juanmcasillas/CatFeederPrototype/CAD/datasheets/funcion_motor_l293d.png

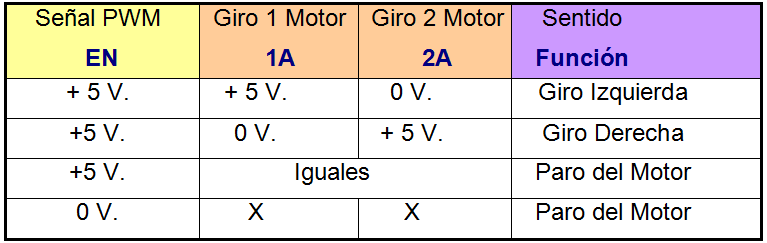
CAD/datasheets/funcion_motor_l293d.png
