juanmcasillas/CatFeederPrototype/CAD/datasheets/l293d.png

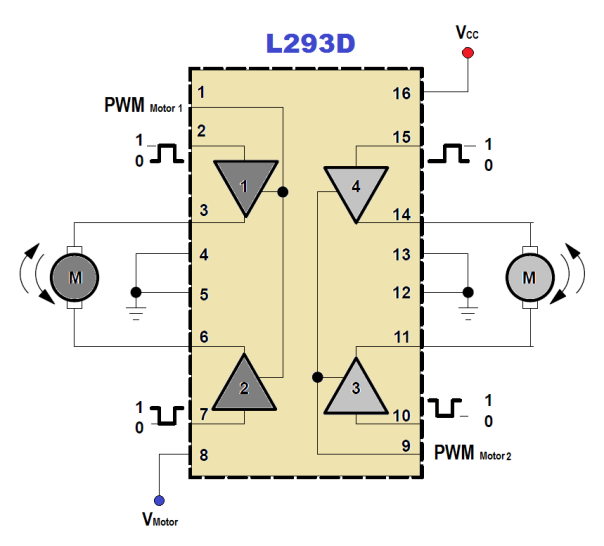
CAD/datasheets/l293d.png
