juanmcasillas/CatFeederPrototype/python/data/blue_ball.png

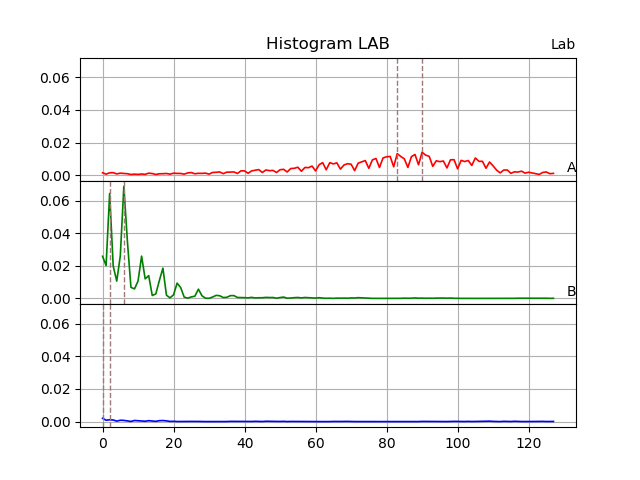
python/data/blue_ball.png
