juanmcasillas/CatFeederPrototype/python/data/eli.png

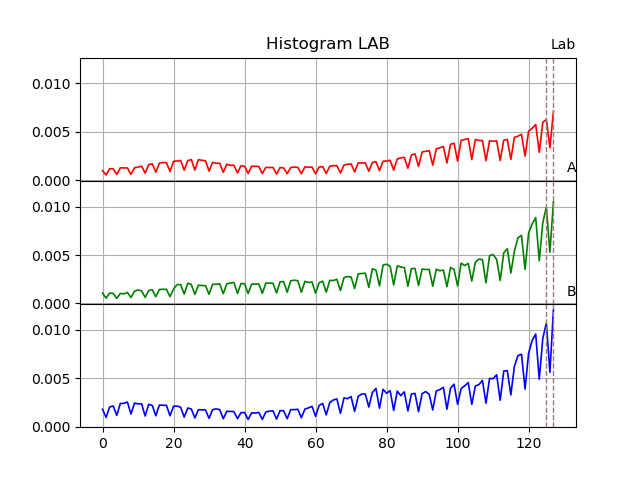
python/data/eli.png
