juanmcasillas/CatFeederPrototype/python/data/firulais.png

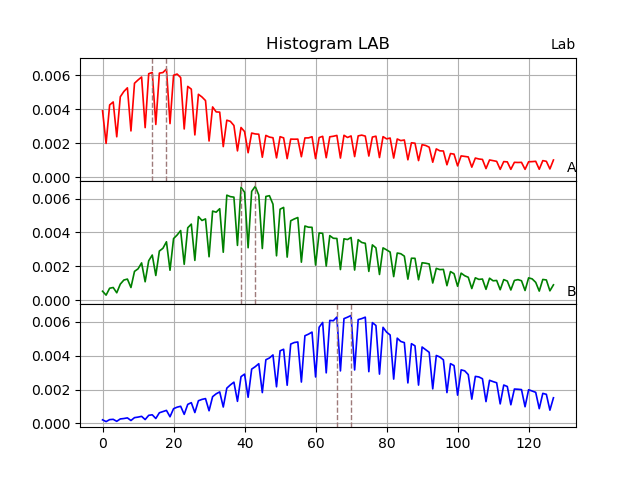
python/data/firulais.png
