juanmcasillas/CatFeederPrototype/python/webserver/www/photos/trans/eli.png

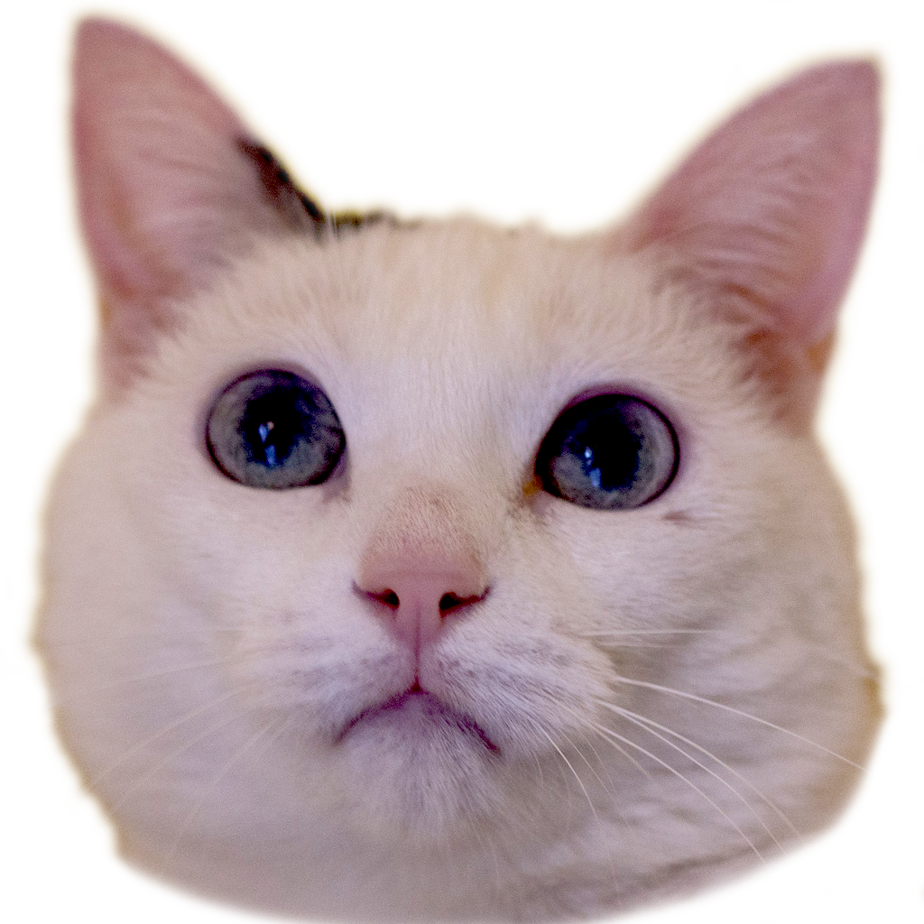
python/webserver/www/photos/trans/eli.png
