juanmcasillas/CatFeederPrototype/python/webserver/www/photos/trans/firulais.png

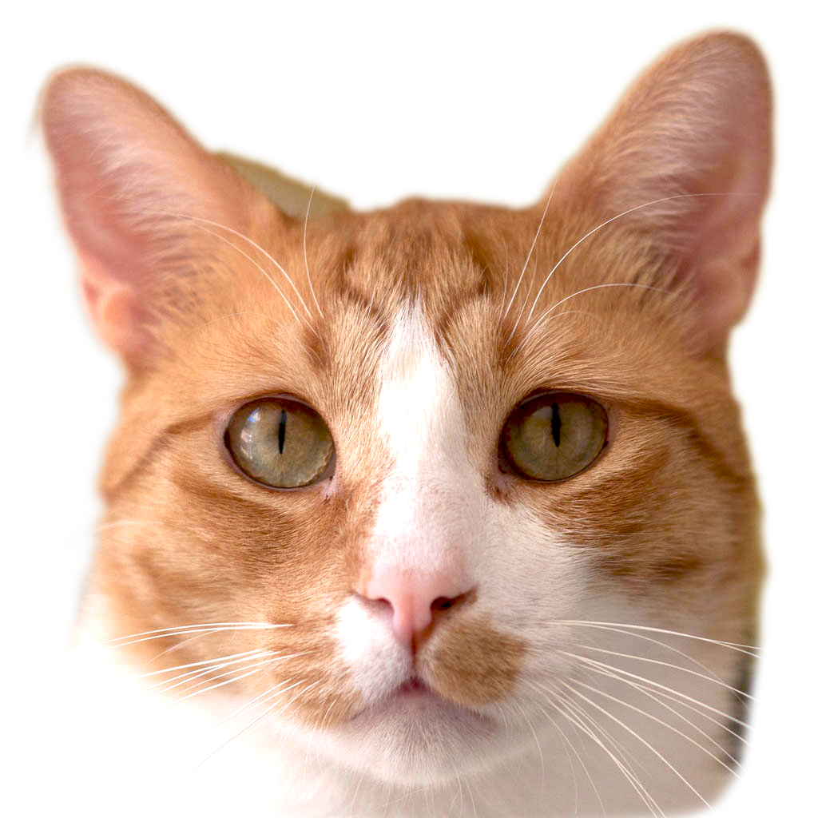
python/webserver/www/photos/trans/firulais.png
