juanmcasillas/CatFeederPrototype/python/webserver/www/snaps/2017/09/15/1505491956.jpg

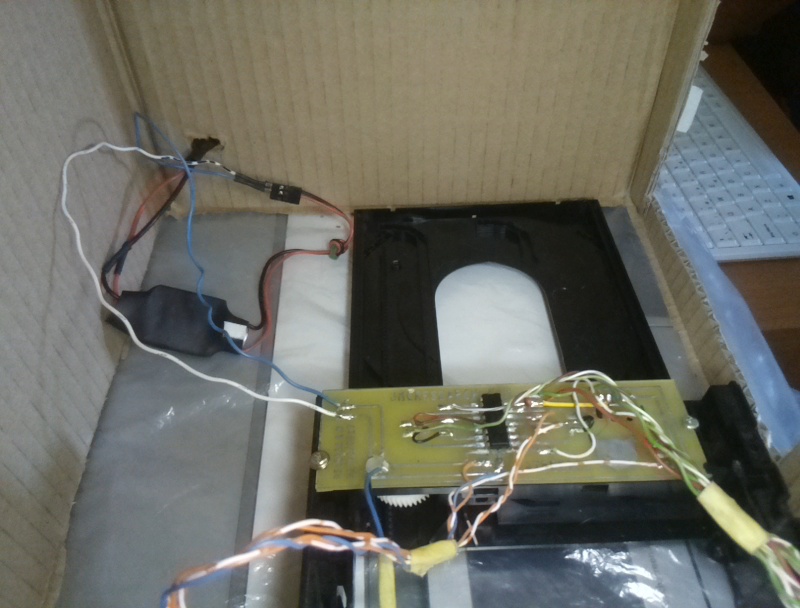
python/webserver/www/snaps/2017/09/15/1505491956.jpg
