juanmcasillas/CatFeederPrototype/python/webserver/www/snaps/2017/09/15/1505492081.jpg

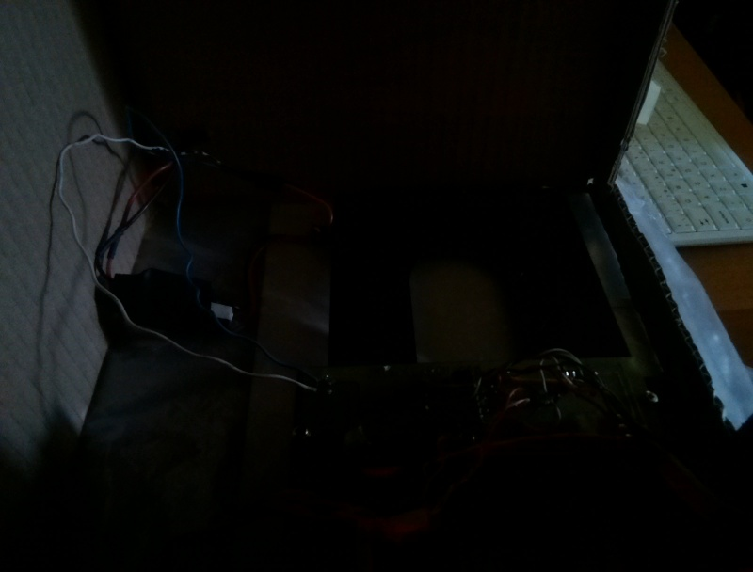
python/webserver/www/snaps/2017/09/15/1505492081.jpg
