juanmcasillas/CatFeederPrototype/python/webserver/www/snaps/2017/09/15/1505498070.jpg

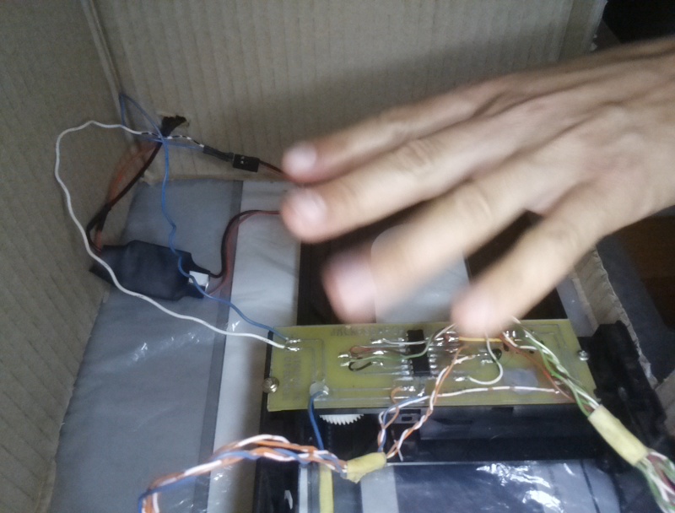
python/webserver/www/snaps/2017/09/15/1505498070.jpg
