juanmcasillas/CatFeederPrototype/python/webserver/www/snaps/2017/09/15/1505506237.jpg

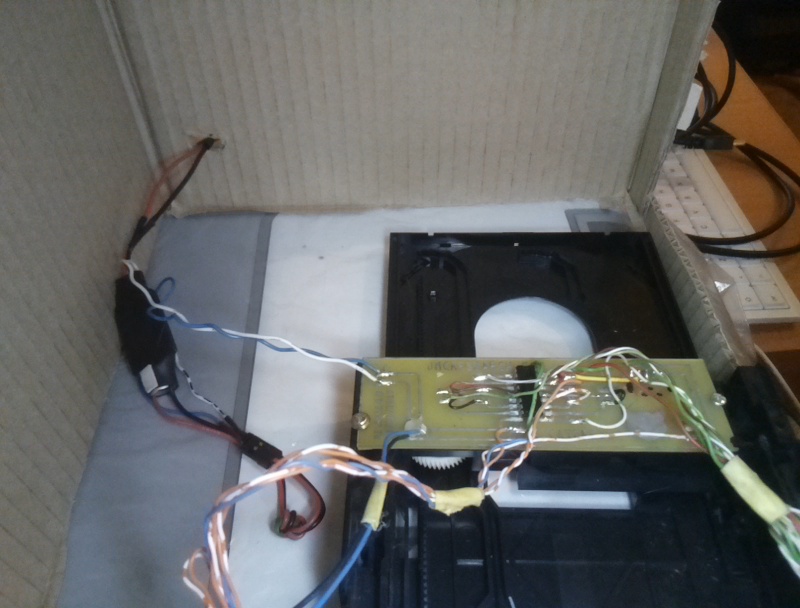
python/webserver/www/snaps/2017/09/15/1505506237.jpg
