juanmcasillas/CatFeederPrototype/python/webserver/www/snaps/2017/09/15/1505513970.jpg

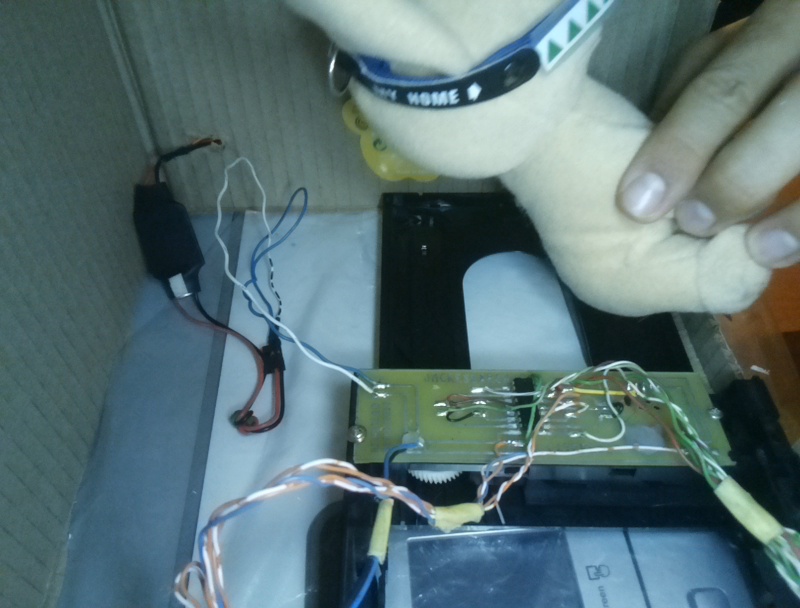
python/webserver/www/snaps/2017/09/15/1505513970.jpg
