juanmcasillas/CatFeederPrototype/python/webserver/www/snaps/2017/09/15/1505515217.jpg

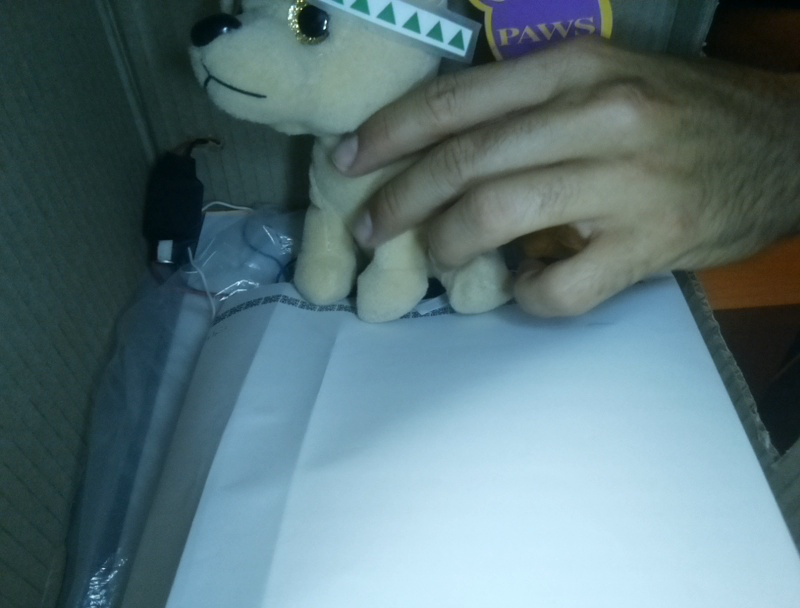
python/webserver/www/snaps/2017/09/15/1505515217.jpg
