juanmcasillas/CatFeederPrototype/python/webserver/www/snaps/2017/09/15/1505515292.jpg

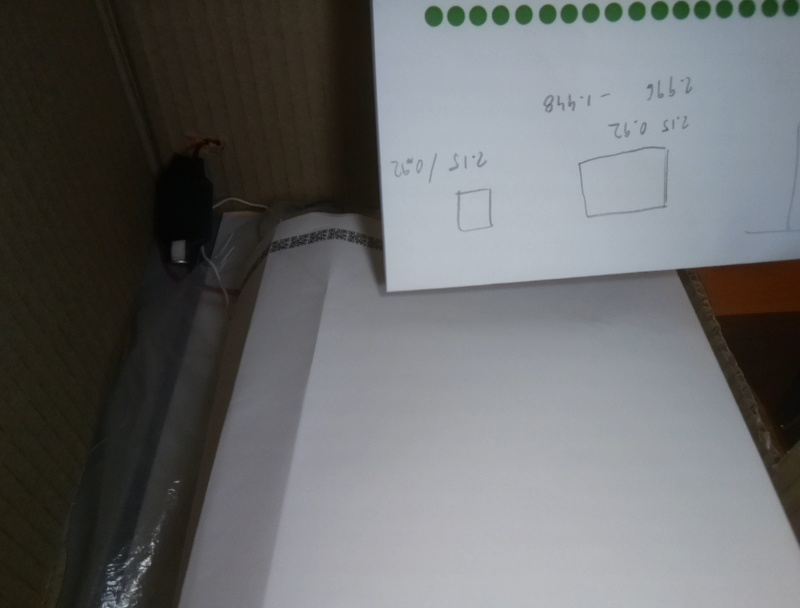
python/webserver/www/snaps/2017/09/15/1505515292.jpg
