juanmcasillas/CatFeederPrototype/python/webserver/www/snaps/2017/09/18/1505749713.jpg

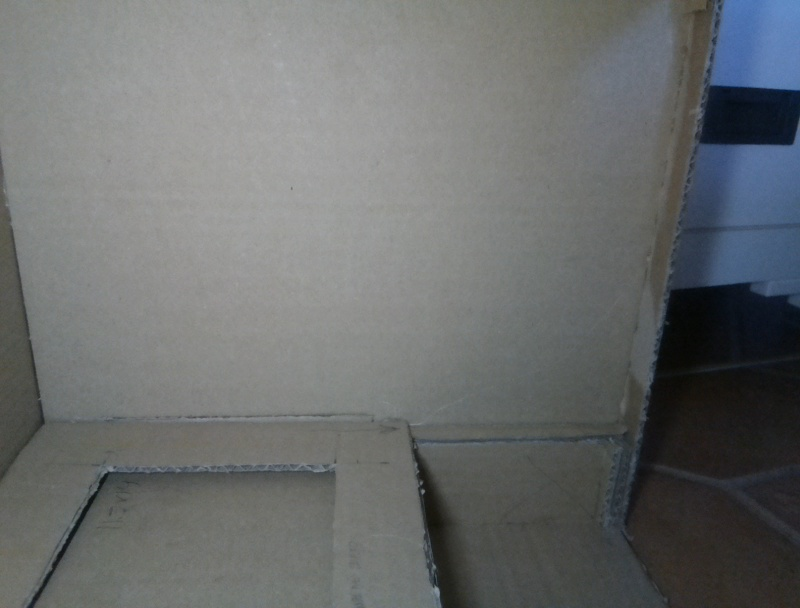
python/webserver/www/snaps/2017/09/18/1505749713.jpg
