juanmcasillas/CatFeederPrototype/python/webserver/www/snaps/2017/10/12/1507797755.png

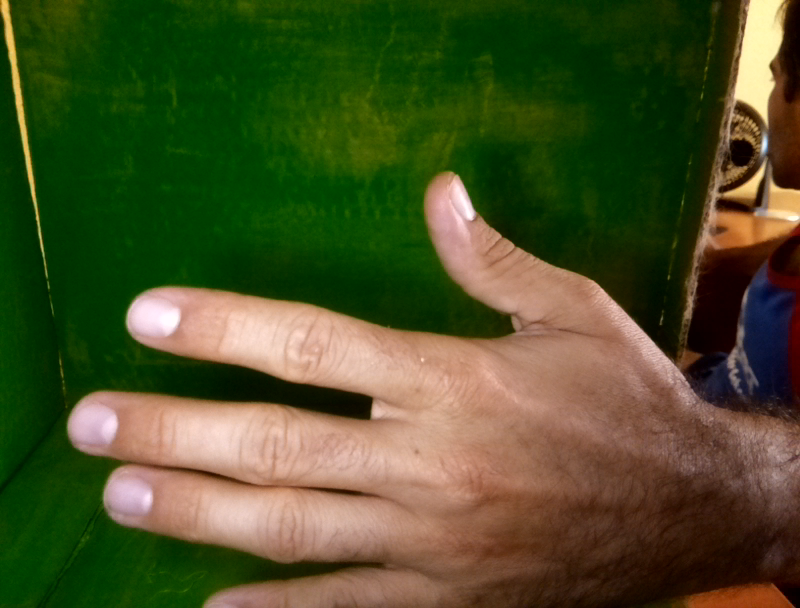
python/webserver/www/snaps/2017/10/12/1507797755.png
