juanmcasillas/CatFeederPrototype/python/webserver/www/snaps/2017/10/12/1507801003.png

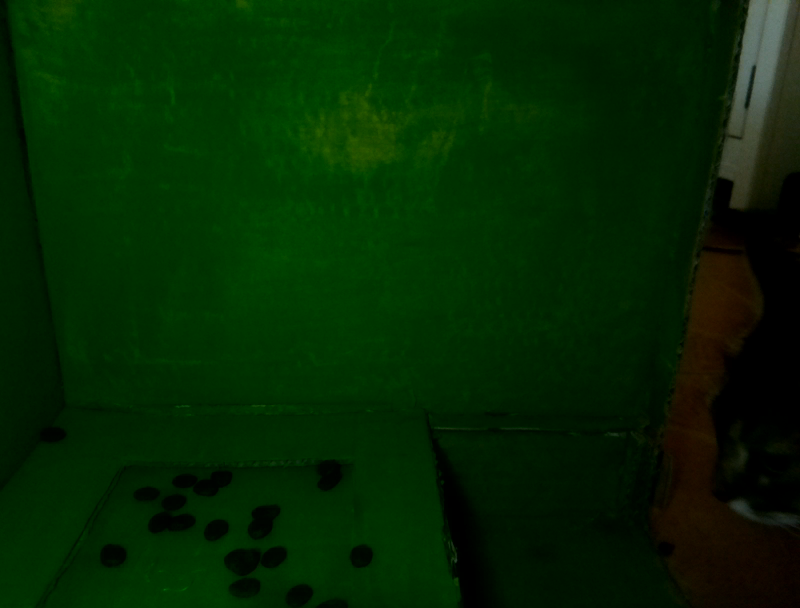
python/webserver/www/snaps/2017/10/12/1507801003.png
