juanmcasillas/CatFeederPrototype/python/webserver/www/snaps/2017/10/12/1507808265.png

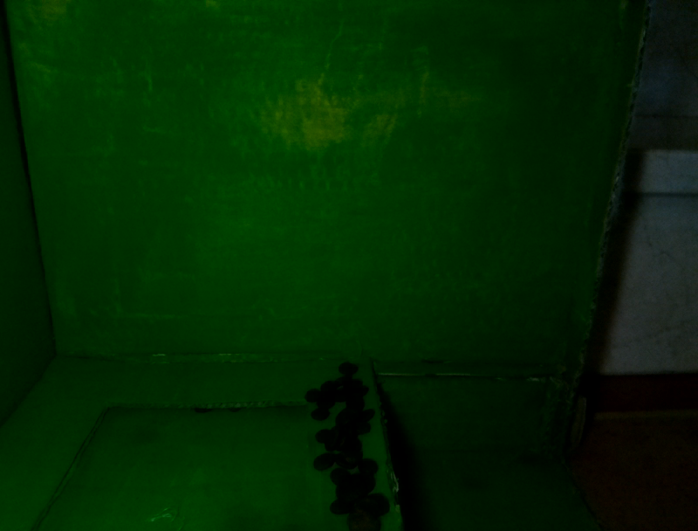
python/webserver/www/snaps/2017/10/12/1507808265.png
