juanmcasillas/CatFeederPrototype/python/webserver/www/snaps/2017/10/12/1507814186.png

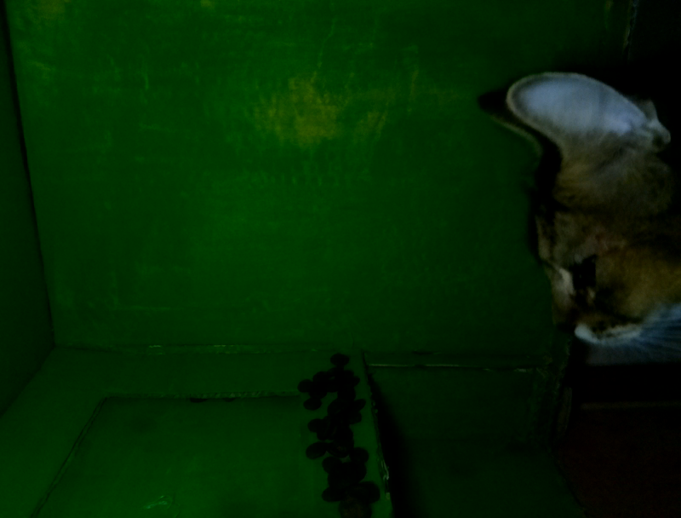
python/webserver/www/snaps/2017/10/12/1507814186.png
