juanmcasillas/CatFeederPrototype/python/webserver/www/snaps/2017/10/12/1507814691.png

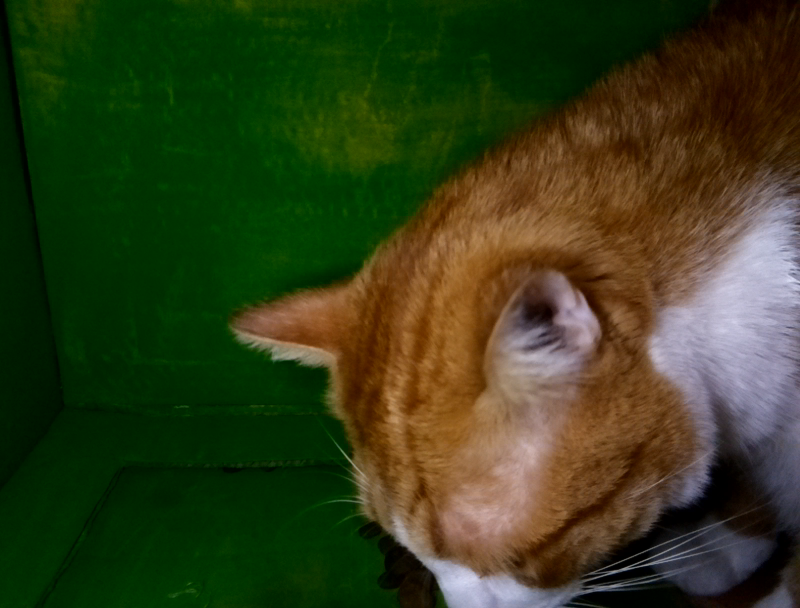
python/webserver/www/snaps/2017/10/12/1507814691.png
