juanmcasillas/CatFeederPrototype/python/webserver/www/snaps/2017/10/12/1507835978.png

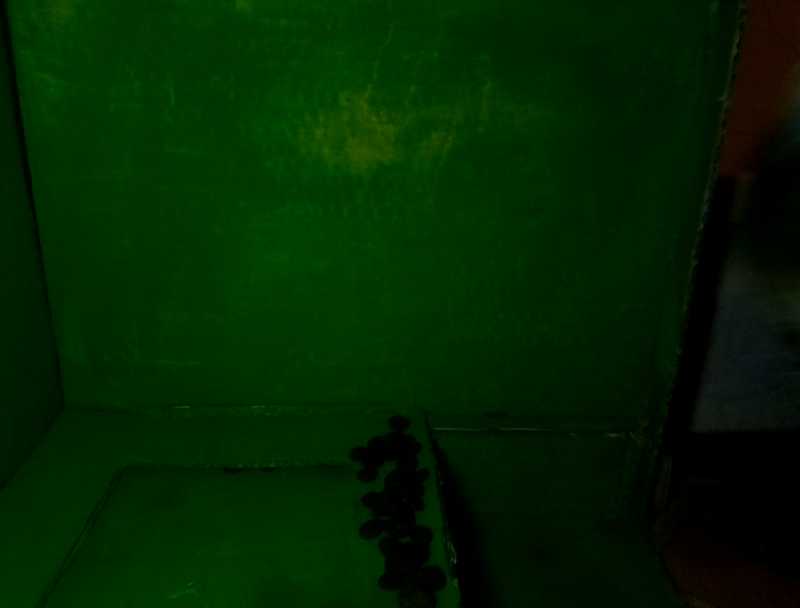
python/webserver/www/snaps/2017/10/12/1507835978.png
