juanmcasillas/CatFeederPrototype/python/webserver/www/snaps/2017/10/13/1507872299.png

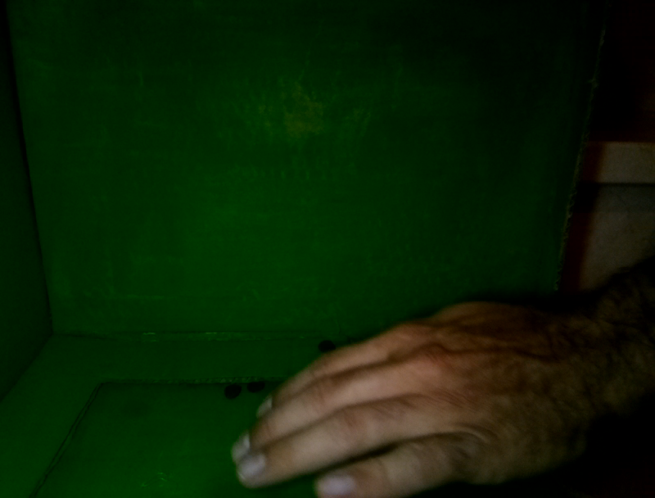
python/webserver/www/snaps/2017/10/13/1507872299.png
