juanmcasillas/CatFeederPrototype/python/webserver/www/snaps/2017/10/13/1507872304.png

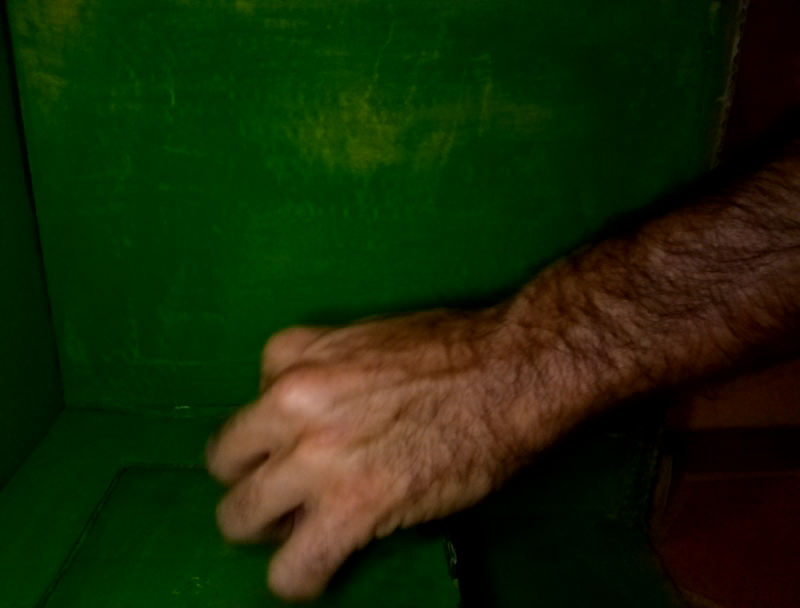
python/webserver/www/snaps/2017/10/13/1507872304.png
