juanmcasillas/CatFeederPrototype/python/webserver/www/snaps/2017/10/13/1507873627.png

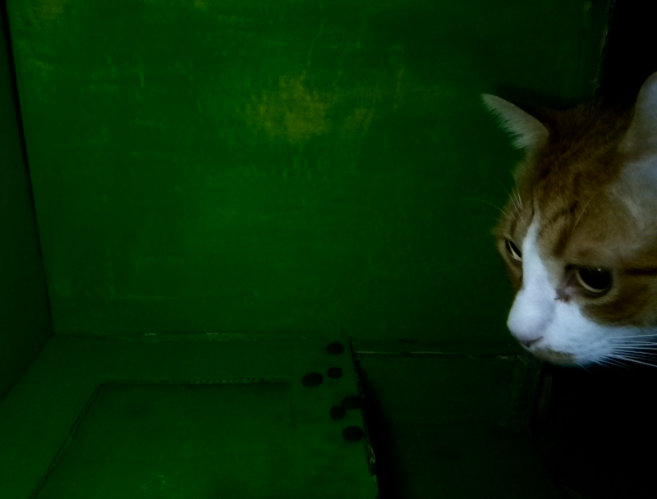
python/webserver/www/snaps/2017/10/13/1507873627.png
