juanmcasillas/CatFeederPrototype/python/webserver/www/snaps/2017/10/14/1507965277.png

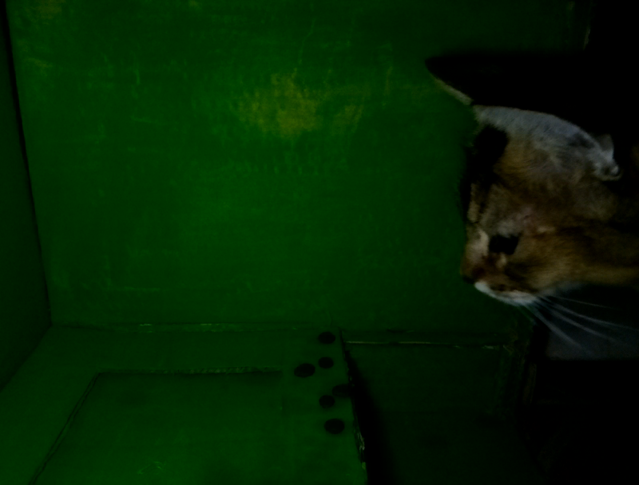
python/webserver/www/snaps/2017/10/14/1507965277.png
