juanmcasillas/CatFeederPrototype/python/webserver/www/snaps/2017/10/14/1507967059.png

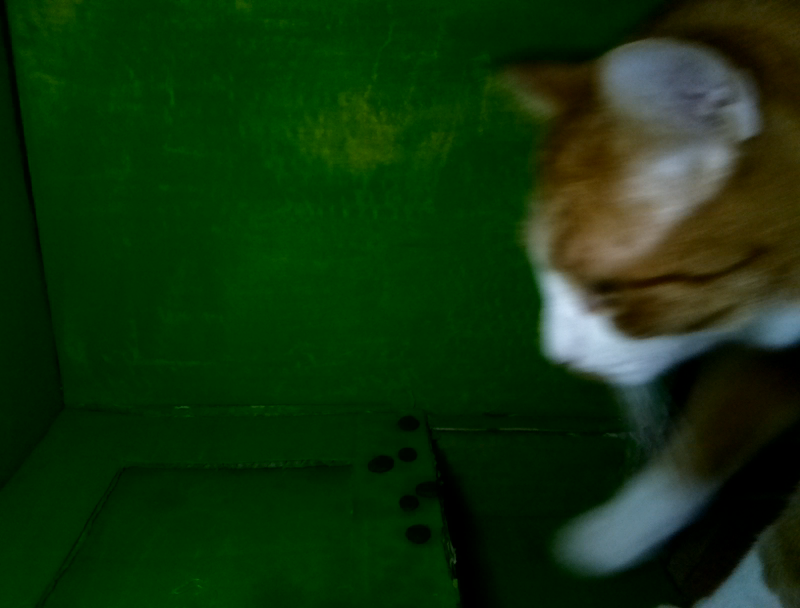
python/webserver/www/snaps/2017/10/14/1507967059.png
