juanmcasillas/CatFeederPrototype/python/webserver/www/snaps/2017/10/14/1507967062.png

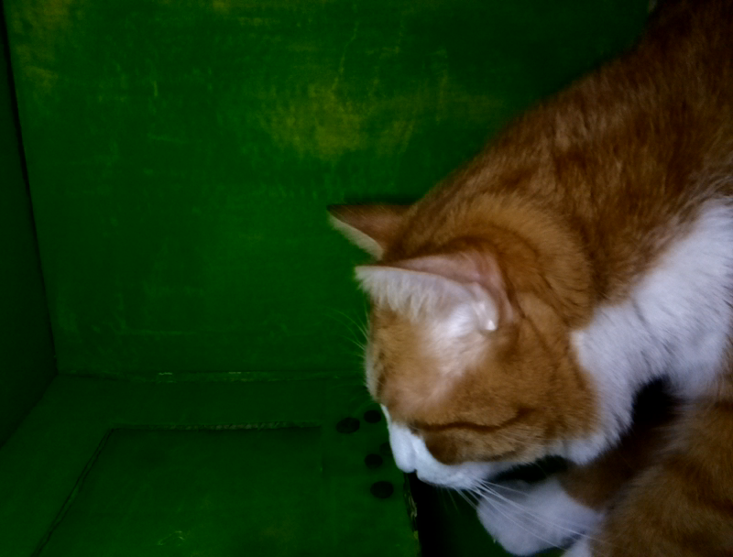
python/webserver/www/snaps/2017/10/14/1507967062.png
