juanmcasillas/CatFeederPrototype/python/webserver/www/snaps/2017/10/14/1507967931.png

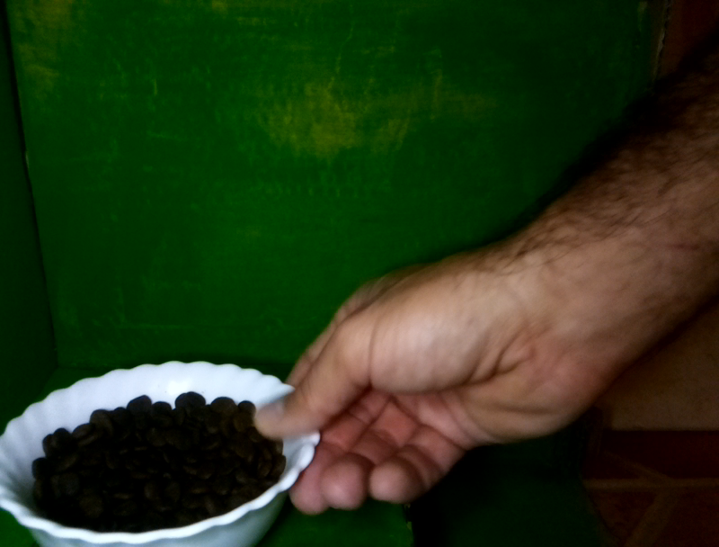
python/webserver/www/snaps/2017/10/14/1507967931.png
