juanmcasillas/CatFeederPrototype/python/webserver/www/snaps/2017/10/14/1507974870.png

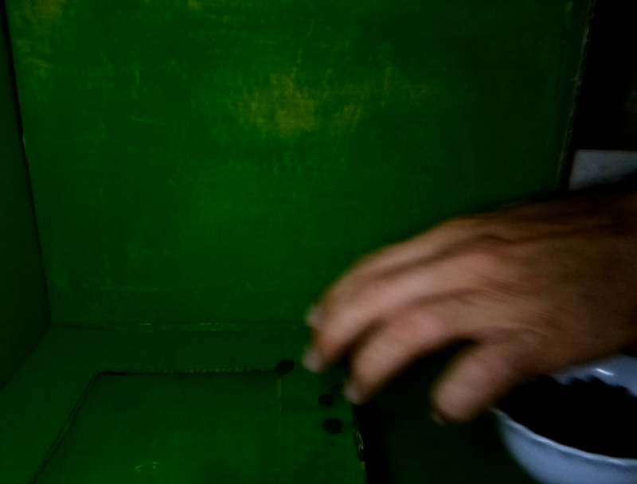
python/webserver/www/snaps/2017/10/14/1507974870.png
