juanmcasillas/CatFeederPrototype/python/webserver/www/snaps/2017/10/14/1507982404.png

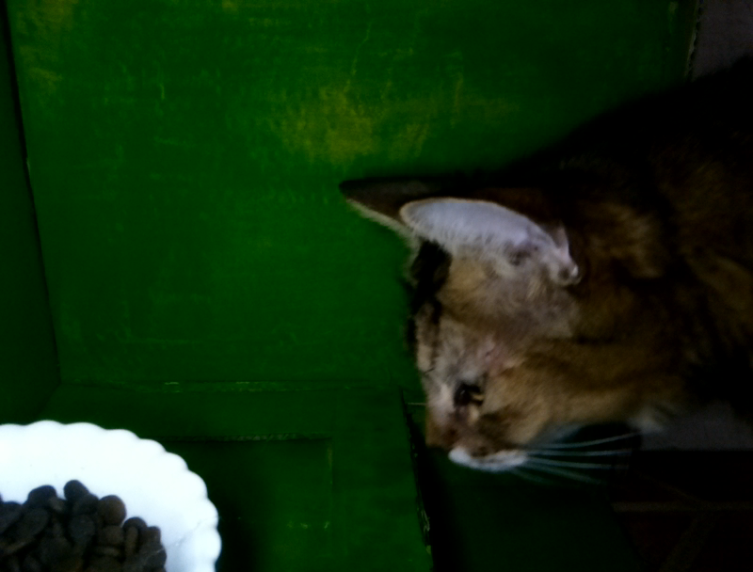
python/webserver/www/snaps/2017/10/14/1507982404.png
