juanmcasillas/CatFeederPrototype/python/webserver/www/snaps/2017/10/14/1507985400.png

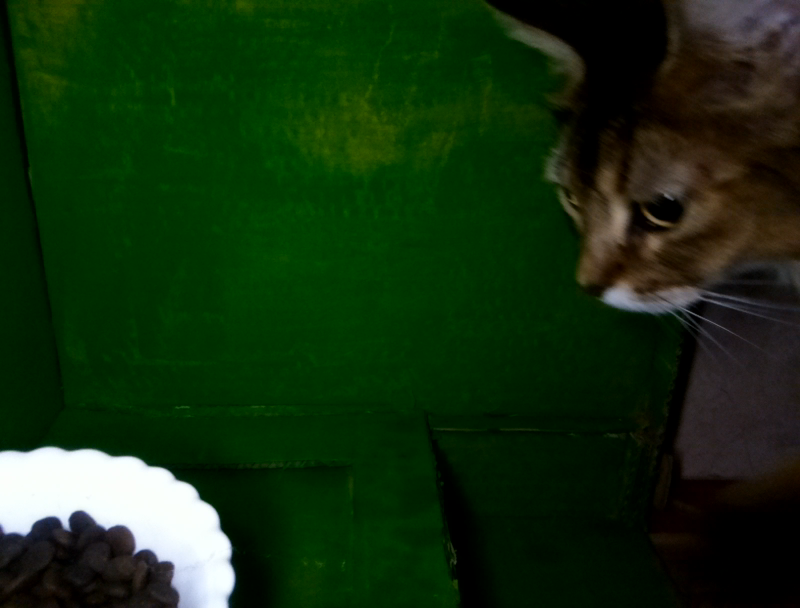
python/webserver/www/snaps/2017/10/14/1507985400.png
