juanmcasillas/CatFeederPrototype/python/webserver/www/snaps/2017/10/14/1507995303.png

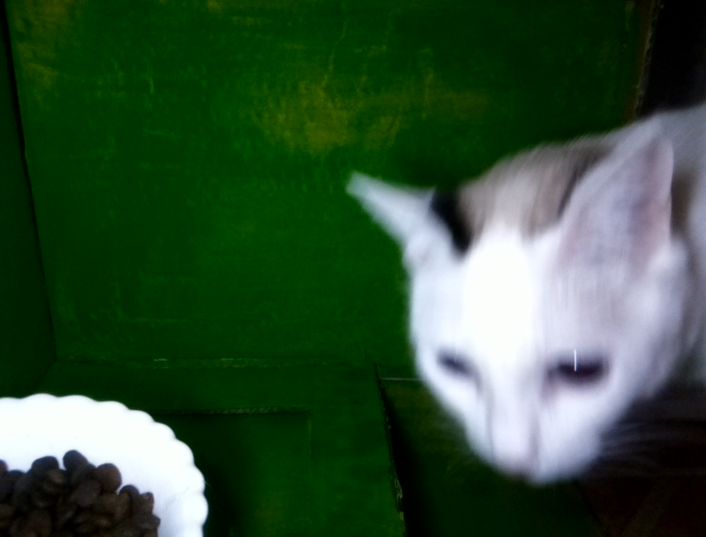
python/webserver/www/snaps/2017/10/14/1507995303.png
