juanmcasillas/CatFeederPrototype/python/webserver/www/snaps/2017/10/14/1508004973.png

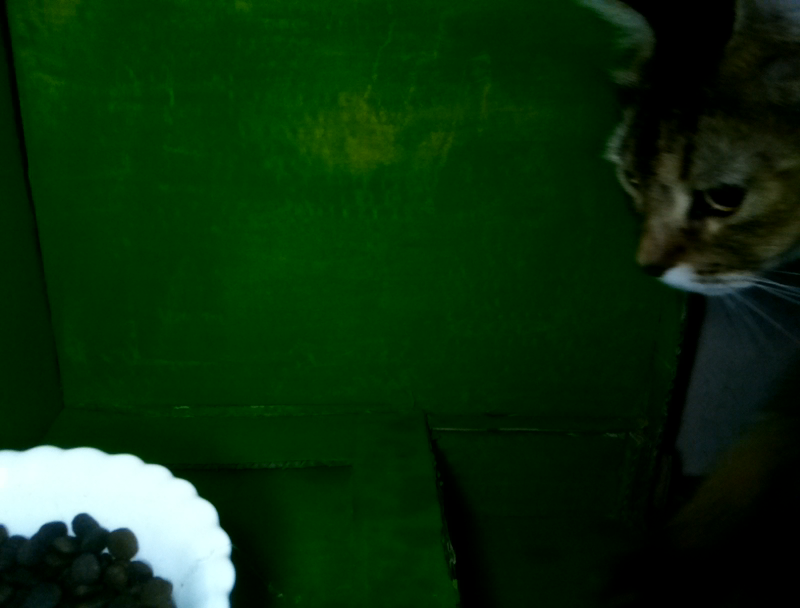
python/webserver/www/snaps/2017/10/14/1508004973.png
