juanmcasillas/CatFeederPrototype/python/webserver/www/snaps/2017/10/14/1508007424.png

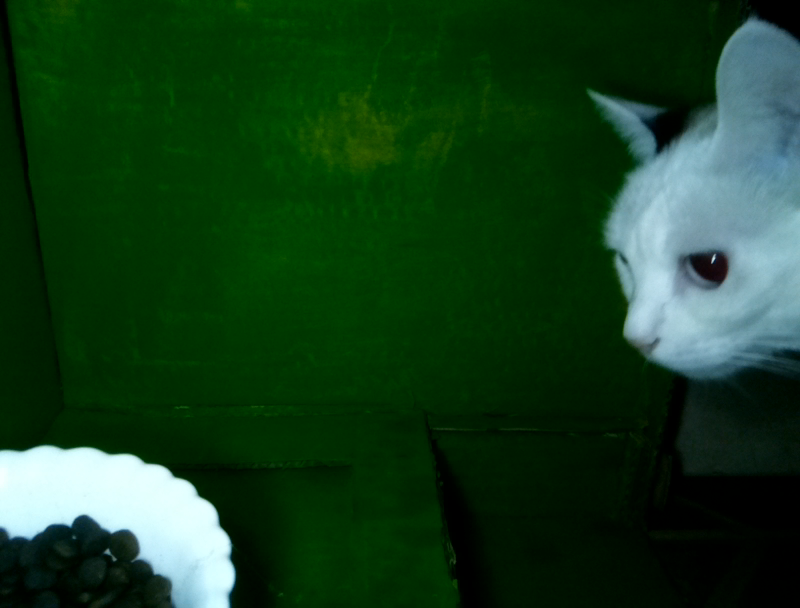
python/webserver/www/snaps/2017/10/14/1508007424.png
