juanmcasillas/CatFeederPrototype/python/webserver/www/snaps/2017/10/15/1508018659.png

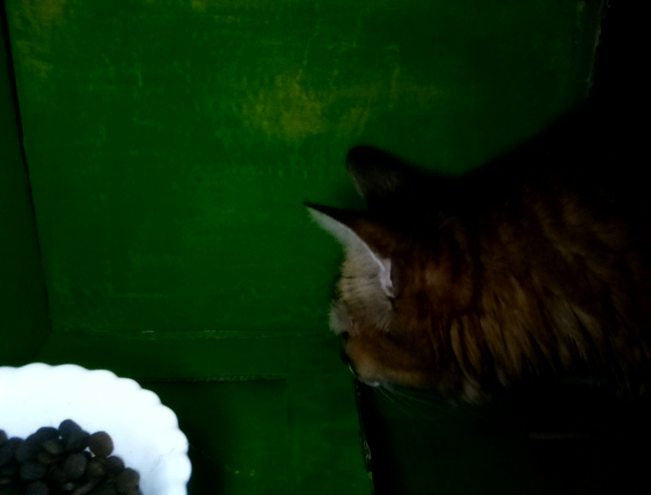
python/webserver/www/snaps/2017/10/15/1508018659.png
