juanmcasillas/CatFeederPrototype/python/webserver/www/snaps/2017/10/15/1508057400.png

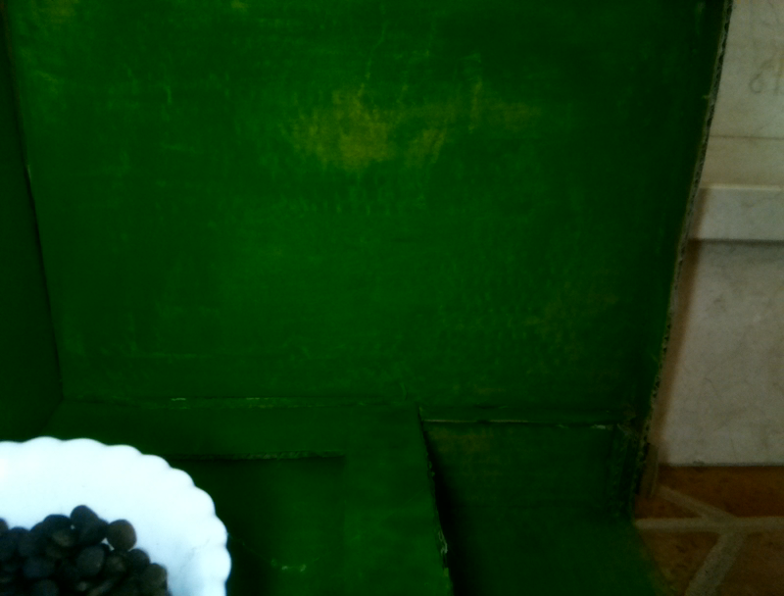
python/webserver/www/snaps/2017/10/15/1508057400.png
