juanmcasillas/CatFeederPrototype/python/webserver/www/snaps/2017/10/15/1508081175.png

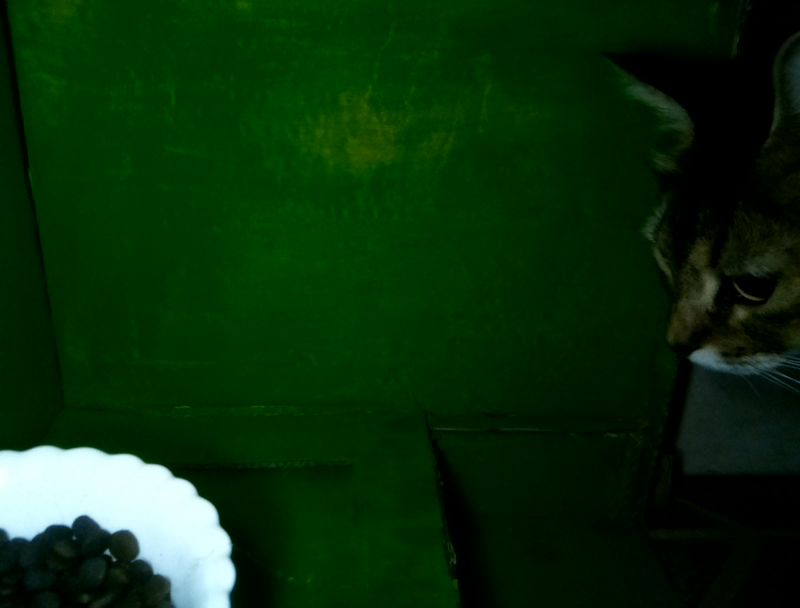
python/webserver/www/snaps/2017/10/15/1508081175.png
