juanmcasillas/CatFeederPrototype/python/webserver/www/snaps/2017/10/15/1508082414.png

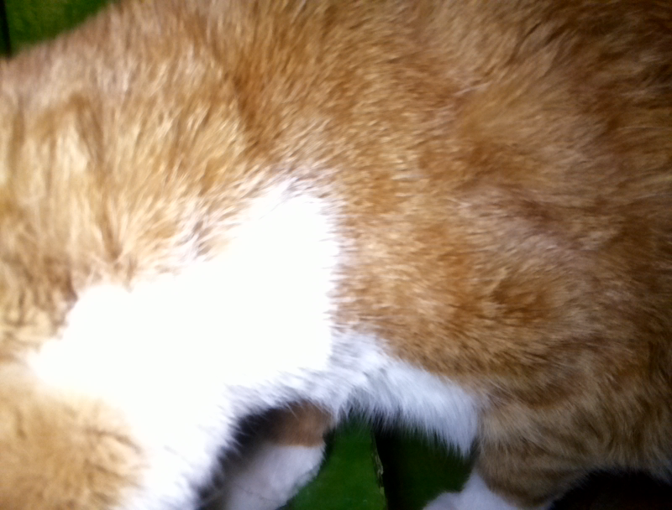
python/webserver/www/snaps/2017/10/15/1508082414.png
