juanmcasillas/CatFeederPrototype/python/webserver/www/snaps/2017/10/15/1508094019.png

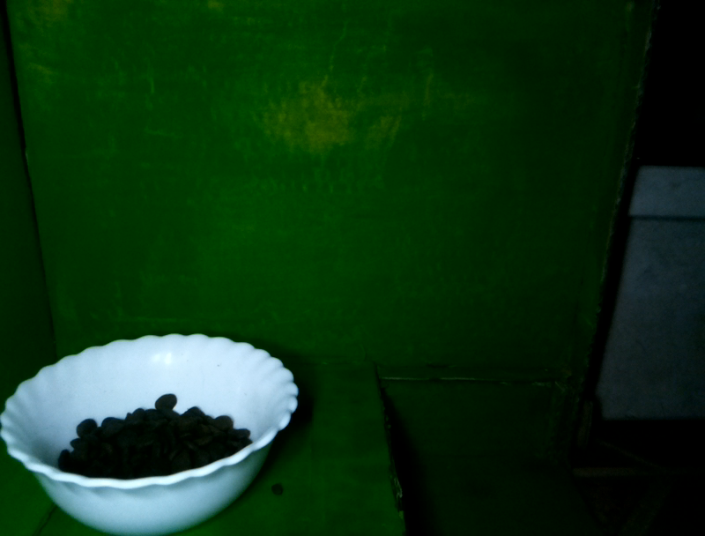
python/webserver/www/snaps/2017/10/15/1508094019.png
