juanmcasillas/CatFeederPrototype/python/webserver/www/snaps/2017/10/16/1508133024.png

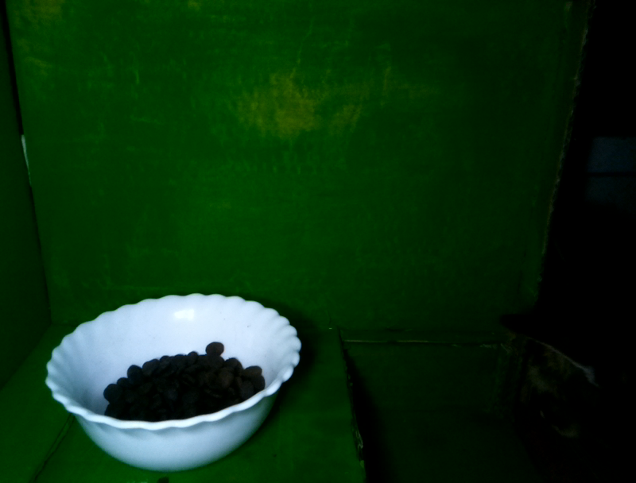
python/webserver/www/snaps/2017/10/16/1508133024.png
