juanmcasillas/CatFeederPrototype/python/webserver/www/snaps/2017/10/16/1508135601.png

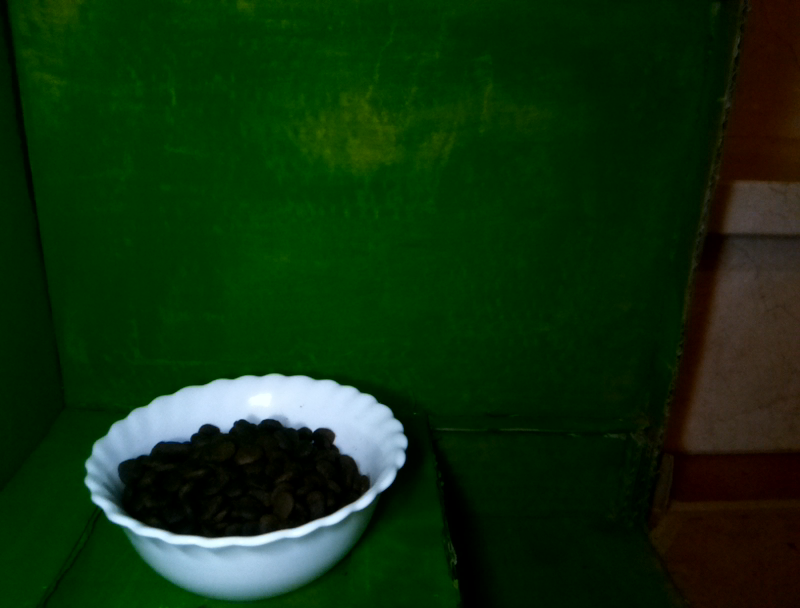
python/webserver/www/snaps/2017/10/16/1508135601.png
