juanmcasillas/CatFeederPrototype/python/webserver/www/snaps/2017/10/16/1508145276.png

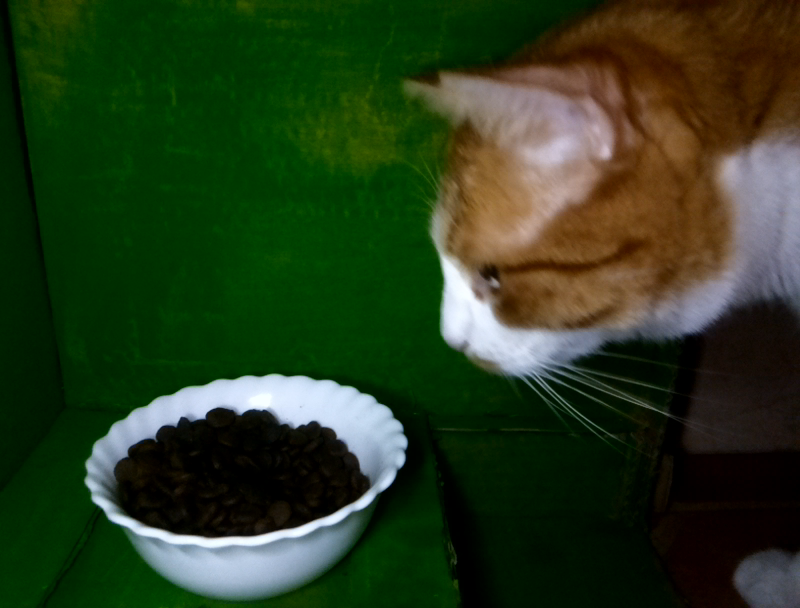
python/webserver/www/snaps/2017/10/16/1508145276.png
