juanmcasillas/CatFeederPrototype/python/webserver/www/snaps/2017/10/16/1508157271.png

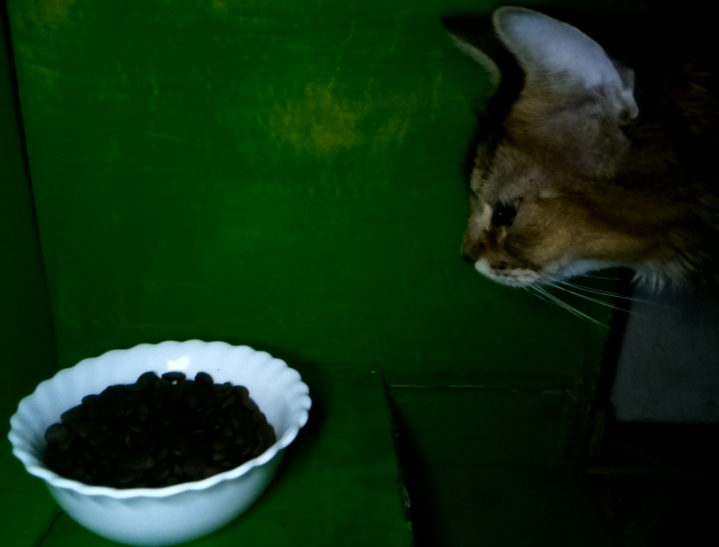
python/webserver/www/snaps/2017/10/16/1508157271.png
