juanmcasillas/CatFeederPrototype/python/webserver/www/snaps/2017/10/16/1508190802.png

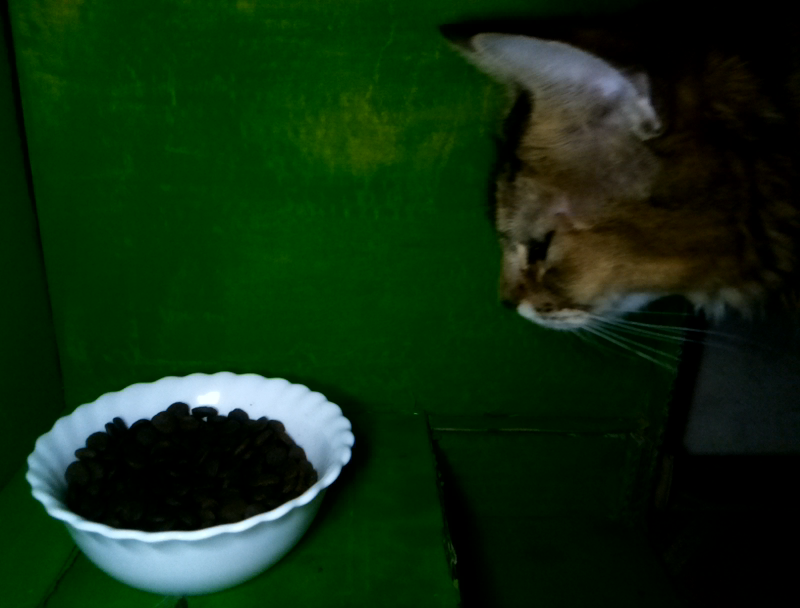
python/webserver/www/snaps/2017/10/16/1508190802.png
