juanmcasillas/CatFeederPrototype/python/webserver/www/snaps/2017/10/17/1508215944.png

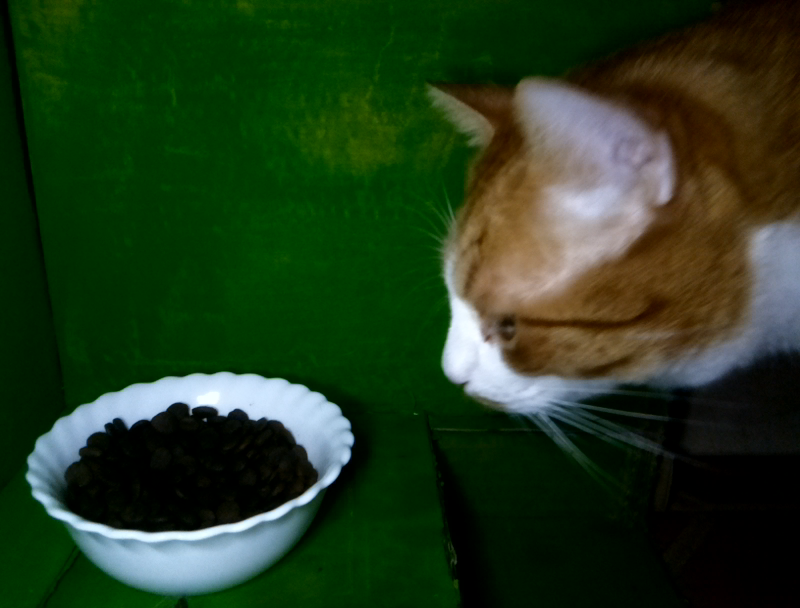
python/webserver/www/snaps/2017/10/17/1508215944.png
