juanmcasillas/CatFeederPrototype/python/webserver/www/snaps/2017/10/17/1508223422.png

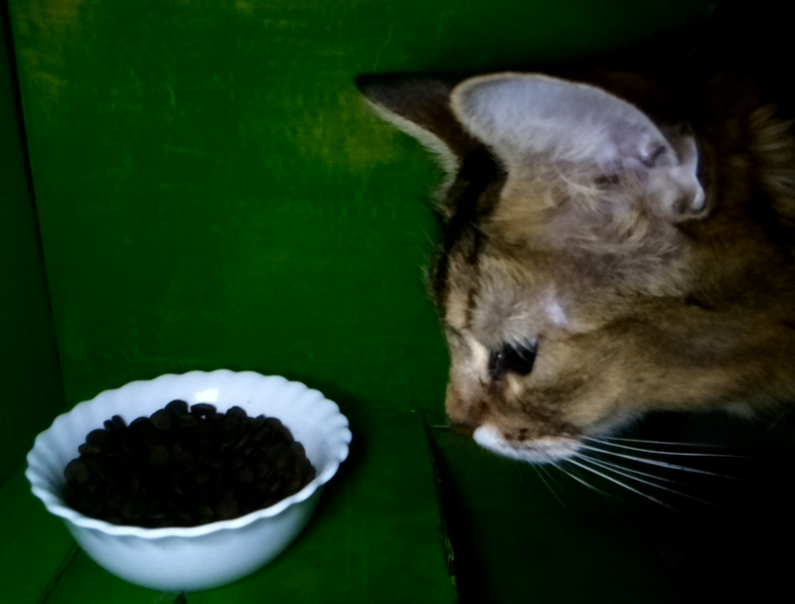
python/webserver/www/snaps/2017/10/17/1508223422.png
