juanmcasillas/CatFeederPrototype/python/webserver/www/snaps/2017/10/17/1508224615.png

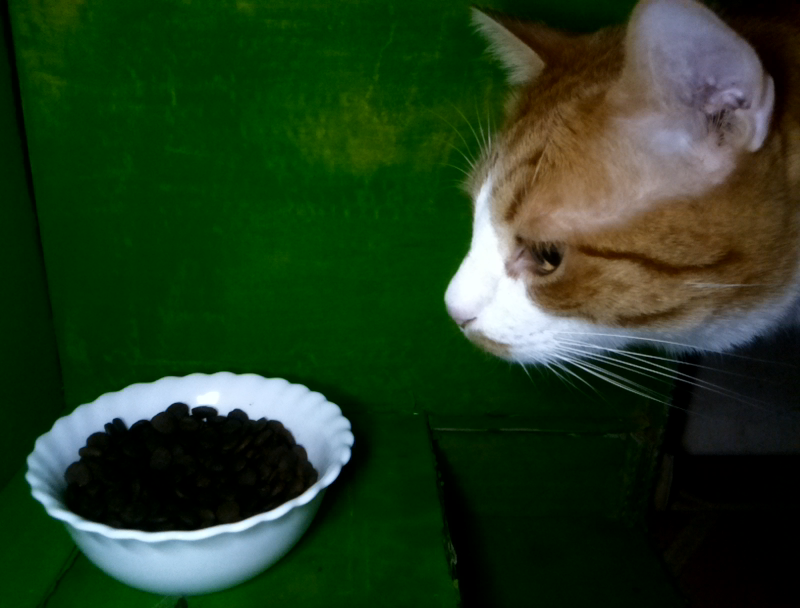
python/webserver/www/snaps/2017/10/17/1508224615.png
