juanmcasillas/CatFeederPrototype/python/webserver/www/snaps/2017/10/17/1508250668.png

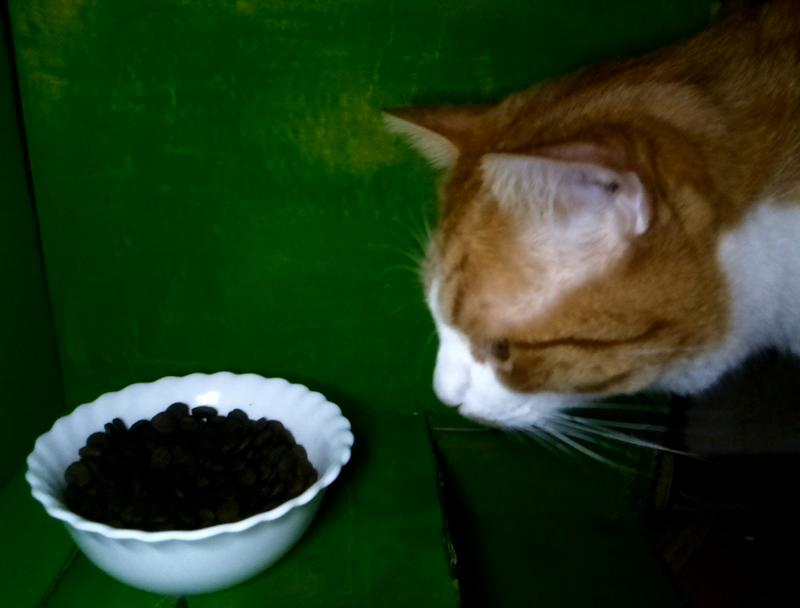
python/webserver/www/snaps/2017/10/17/1508250668.png
