juanmcasillas/CatFeederPrototype/python/webserver/www/snaps/2017/10/18/1508305820.png

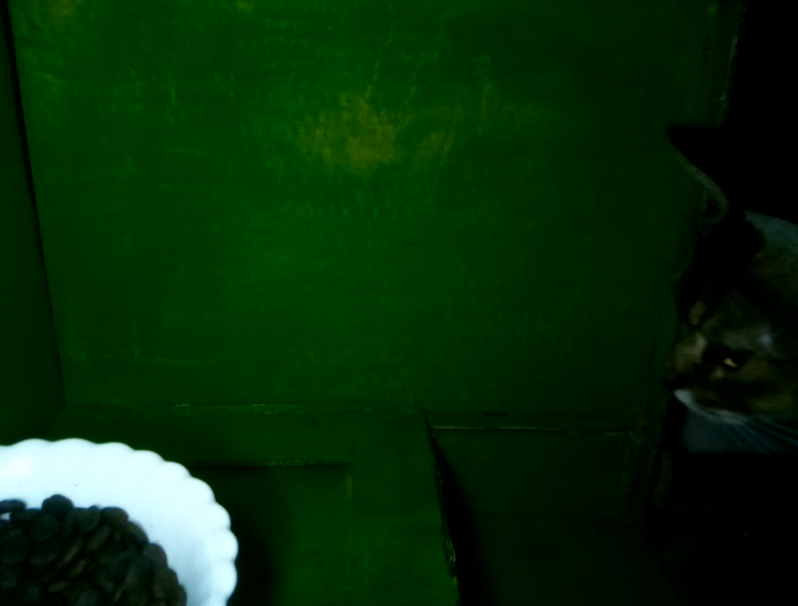
python/webserver/www/snaps/2017/10/18/1508305820.png
