juanmcasillas/CatFeederPrototype/python/webserver/www/snaps/2017/10/18/1508321046.png

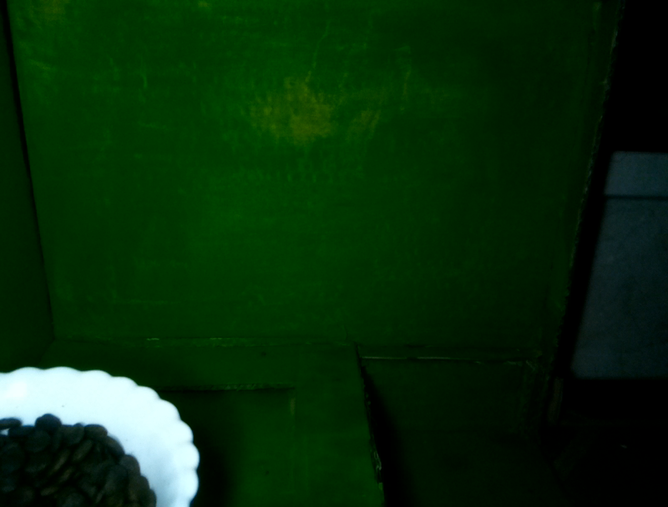
python/webserver/www/snaps/2017/10/18/1508321046.png
